JLU-Automation-Team/spider-robot/doc/2.png

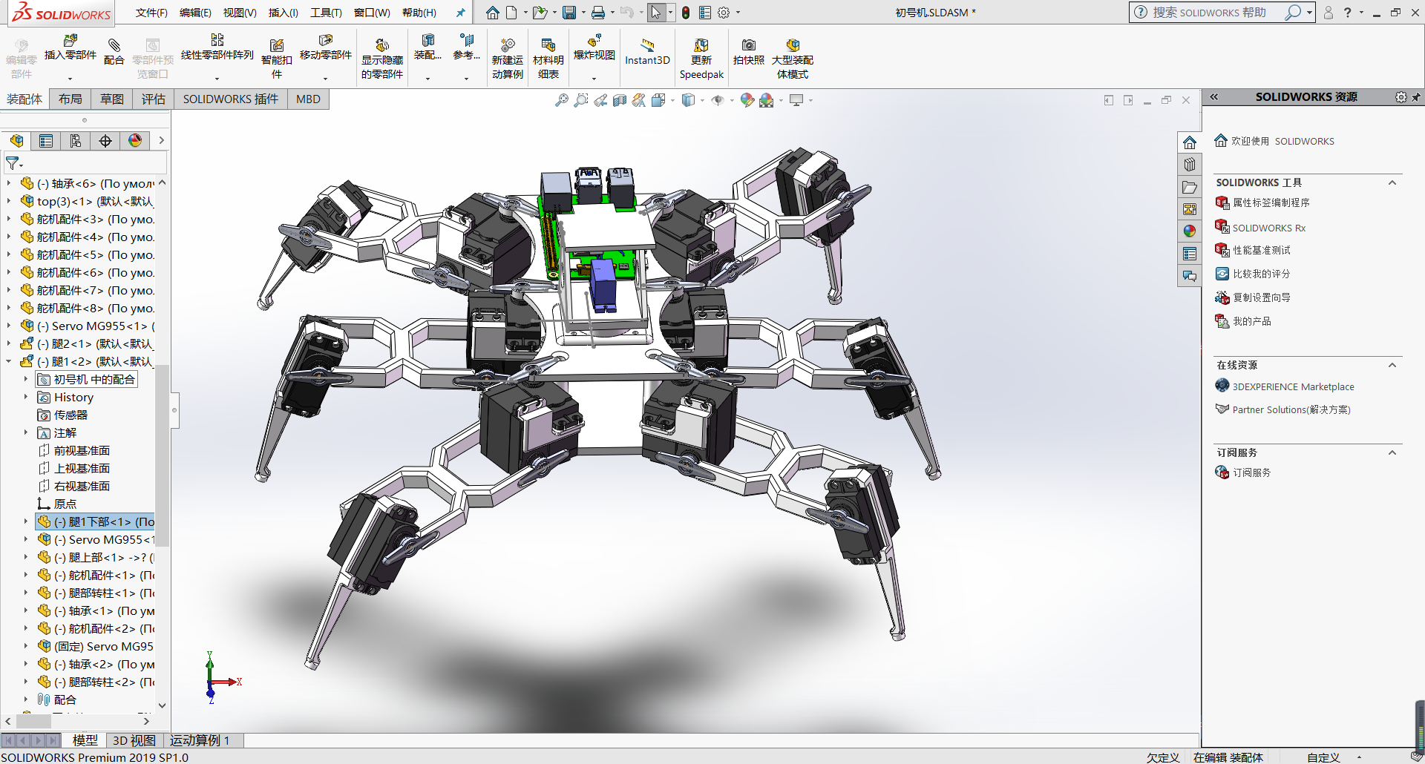
doc/2.png
