JLU-Automation-Team/spider-robot/doc/7.png

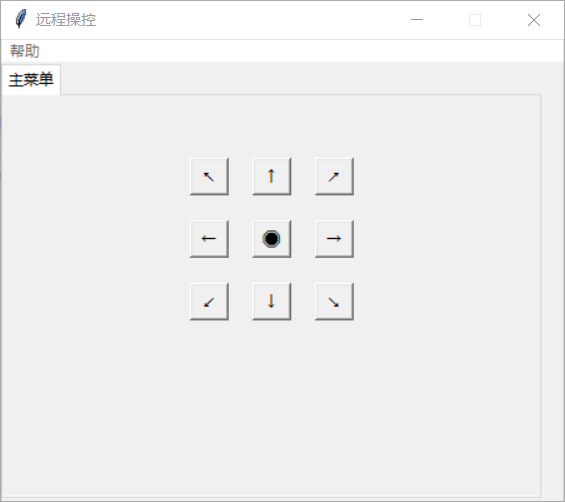
doc/7.png
