JLU-Automation-Team/spider-robot/resource/运动控制相关资料/6.png

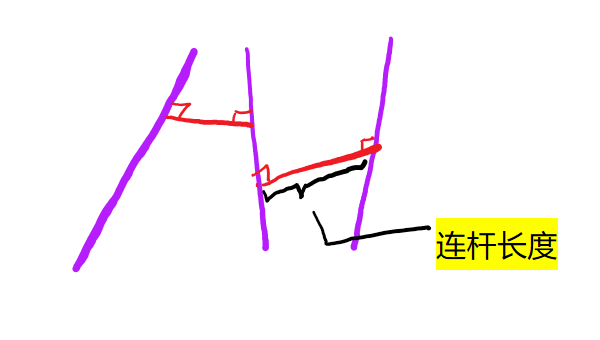
resource/运动控制相关资料/6.png
