JLU-Automation-Team/spider-robot/resource/运动控制相关资料/8.png

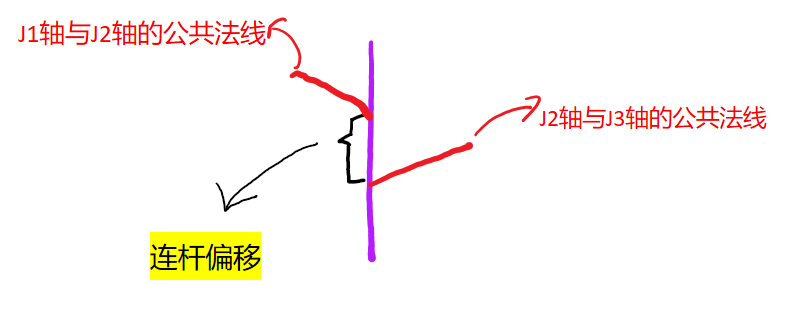
resource/运动控制相关资料/8.png
