JLU-Automation-Team/spider-robot/hardware/机械结构/舵机驱动板示意图.SLDPRT

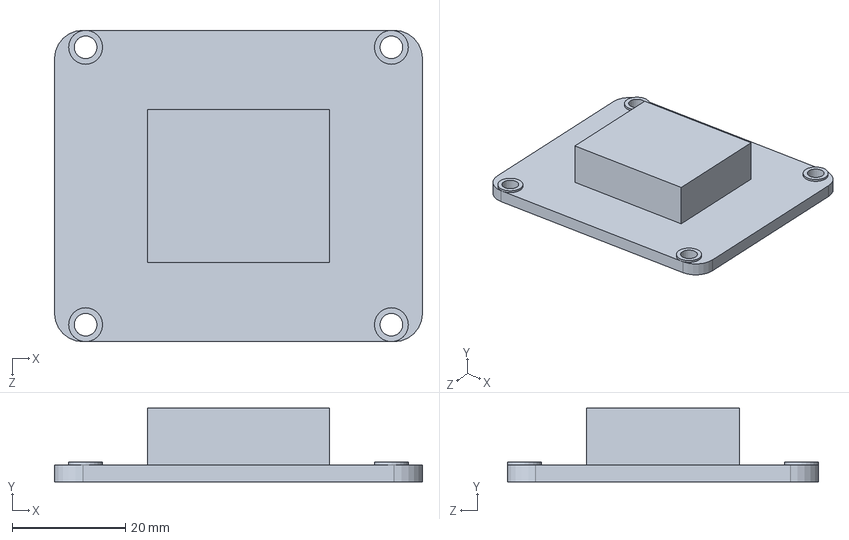
[picture p32: CAD file, 2022-01-22]
hardware/机械结构/舵机驱动板示意图.SLDPRT
65.0 x 13.0 x 55.0 mm
