JLU-Automation-Team/spider-robot/hardware/机械结构/腿2下部.SLDPRT

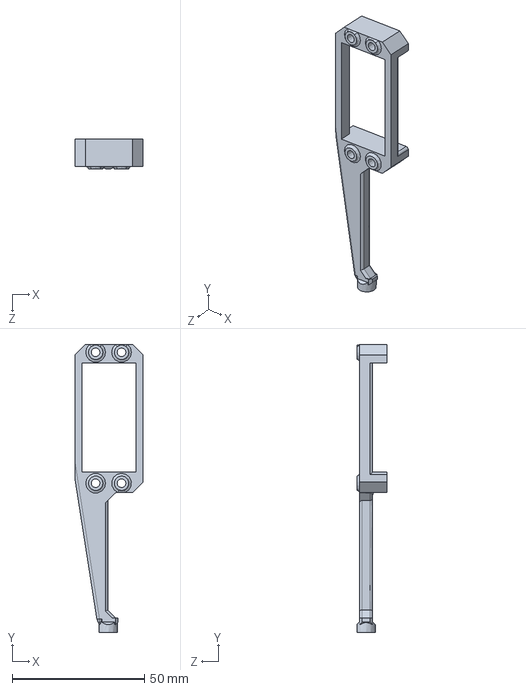
[picture p33: CAD file, 2022-01-22]
hardware/机械结构/腿2下部.SLDPRT
25.9 x 109.0 x 11.5 mm
