JLU-Automation-Team/spider-robot/hardware/机械结构/舵机配件.SLDPRT

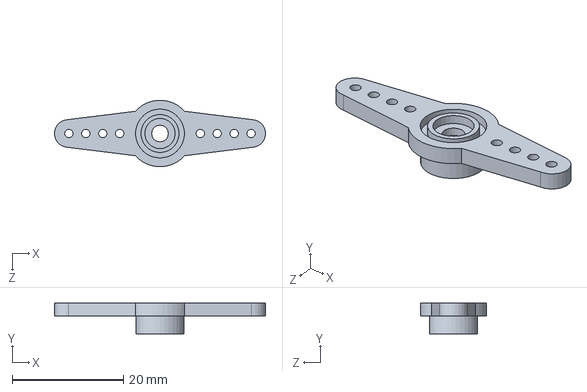
[picture p34: CAD file, 2022-01-22]
hardware/机械结构/舵机配件.SLDPRT
38.0 x 5.50 x 11.9 mm
