JLU-Automation-Team/spider-robot/hardware/机械结构/MG995齿轮.SLDPRT

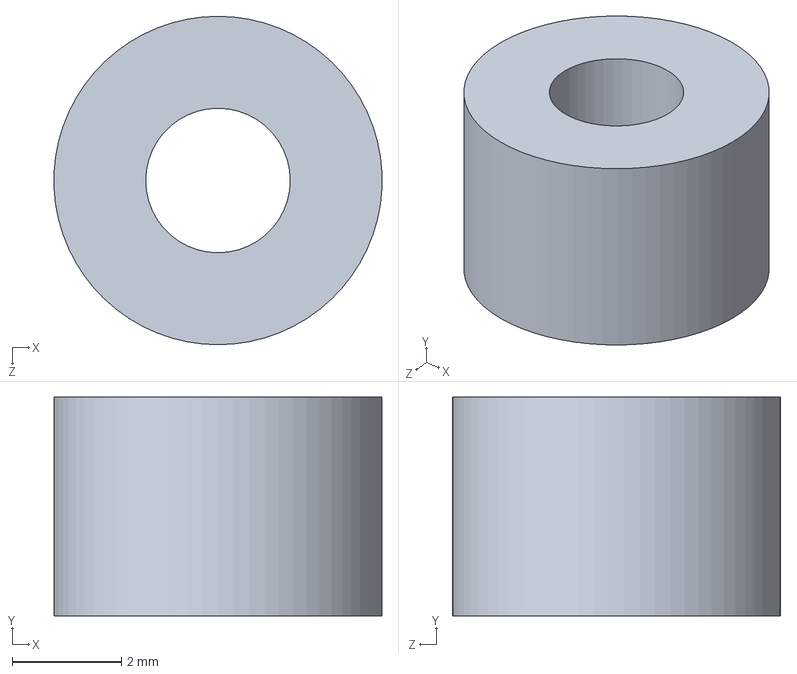
[picture p35: CAD file, 2022-01-22]
hardware/机械结构/MG995齿轮.SLDPRT
5.99 x 4.00 x 6.00 mm
