JLU-Automation-Team/spider-robot/hardware/机械结构/腿上部.SLDPRT

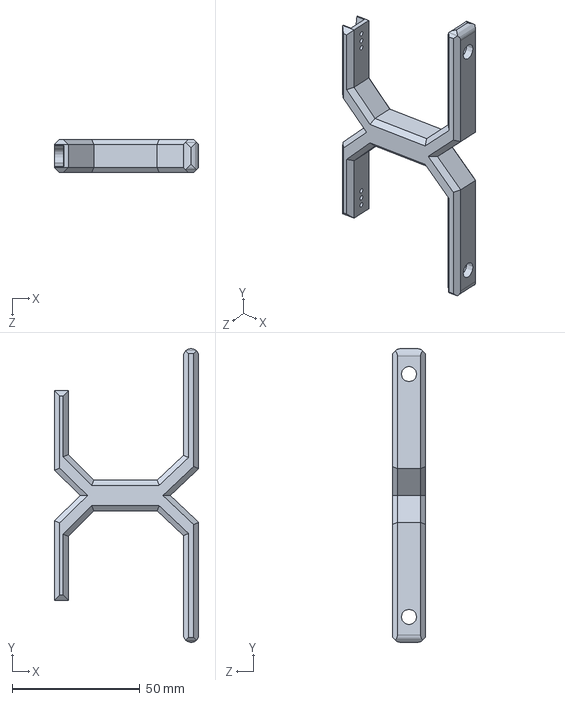
[picture p36: CAD file, 2022-01-22]
hardware/机械结构/腿上部.SLDPRT
56.5 x 115.1 x 13.0 mm
