JLU-Automation-Team/spider-robot/hardware/机械结构/底板支柱.SLDPRT

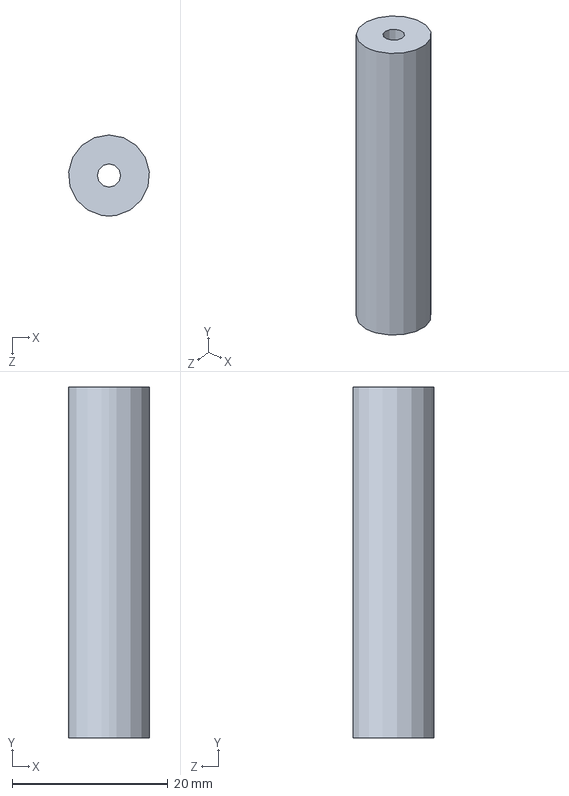
[picture p37: CAD file, 2022-01-22]
hardware/机械结构/底板支柱.SLDPRT
10.4 x 45.0 x 10.4 mm
