JLU-Automation-Team/spider-robot/hardware/机械结构/MG995前板.SLDPRT

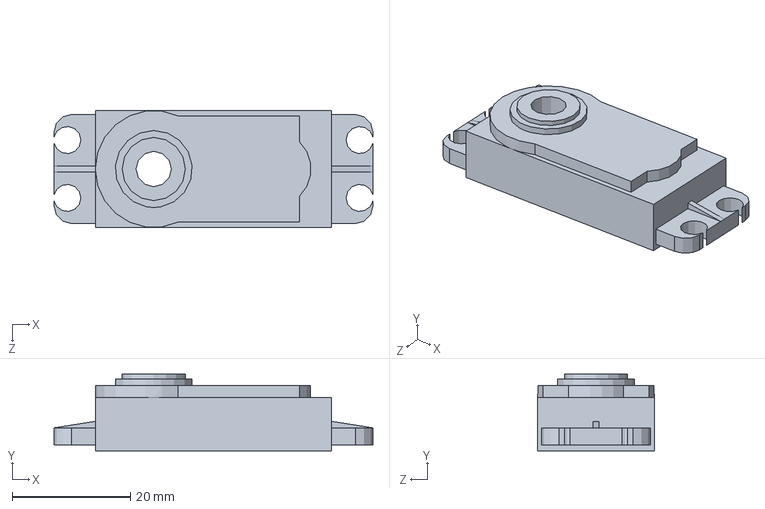
[picture p38: CAD file, 2022-01-22]
hardware/机械结构/MG995前板.SLDPRT
54.0 x 13.0 x 19.8 mm
