JLU-Automation-Team/spider-robot/hardware/机械结构/MG995后板.SLDPRT

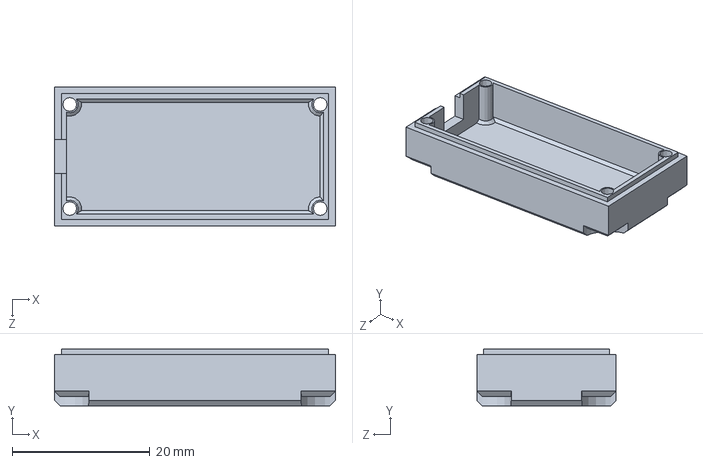
[picture p39: CAD file, 2022-01-22]
hardware/机械结构/MG995后板.SLDPRT
40.7 x 8.25 x 20.2 mm
