JLU-Automation-Team/spider-robot/hardware/机械结构/MG995中板.SLDPRT

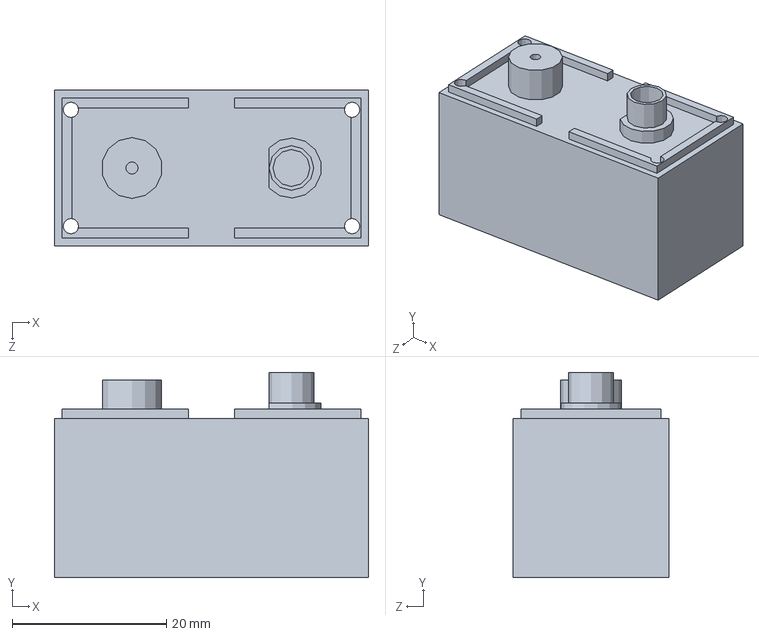
[picture p40: CAD file, 2022-01-22]
hardware/机械结构/MG995中板.SLDPRT
40.8 x 26.6 x 20.2 mm
