JLU-Automation-Team/spider-robot/hardware/机械结构/腿部转柱.SLDPRT

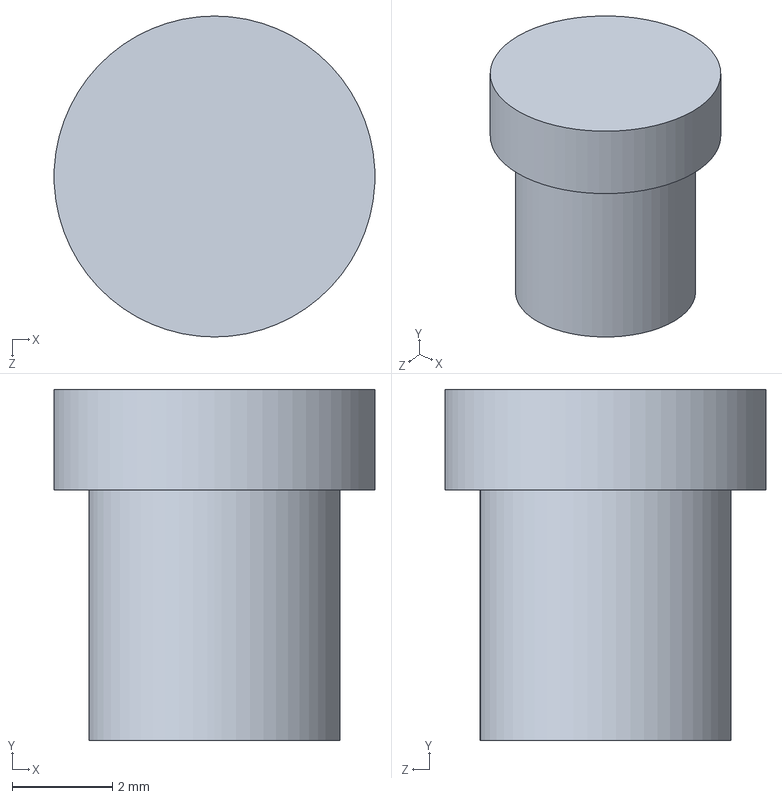
[picture p41: CAD file, 2022-01-22]
hardware/机械结构/腿部转柱.SLDPRT
6.39 x 7.00 x 6.40 mm
